brainsmoke/matrixpad/pcb/matrixpad/matrixpad.sch

## KiCad design pcb/matrixpad/matrixpad.sch (2014-07-25)

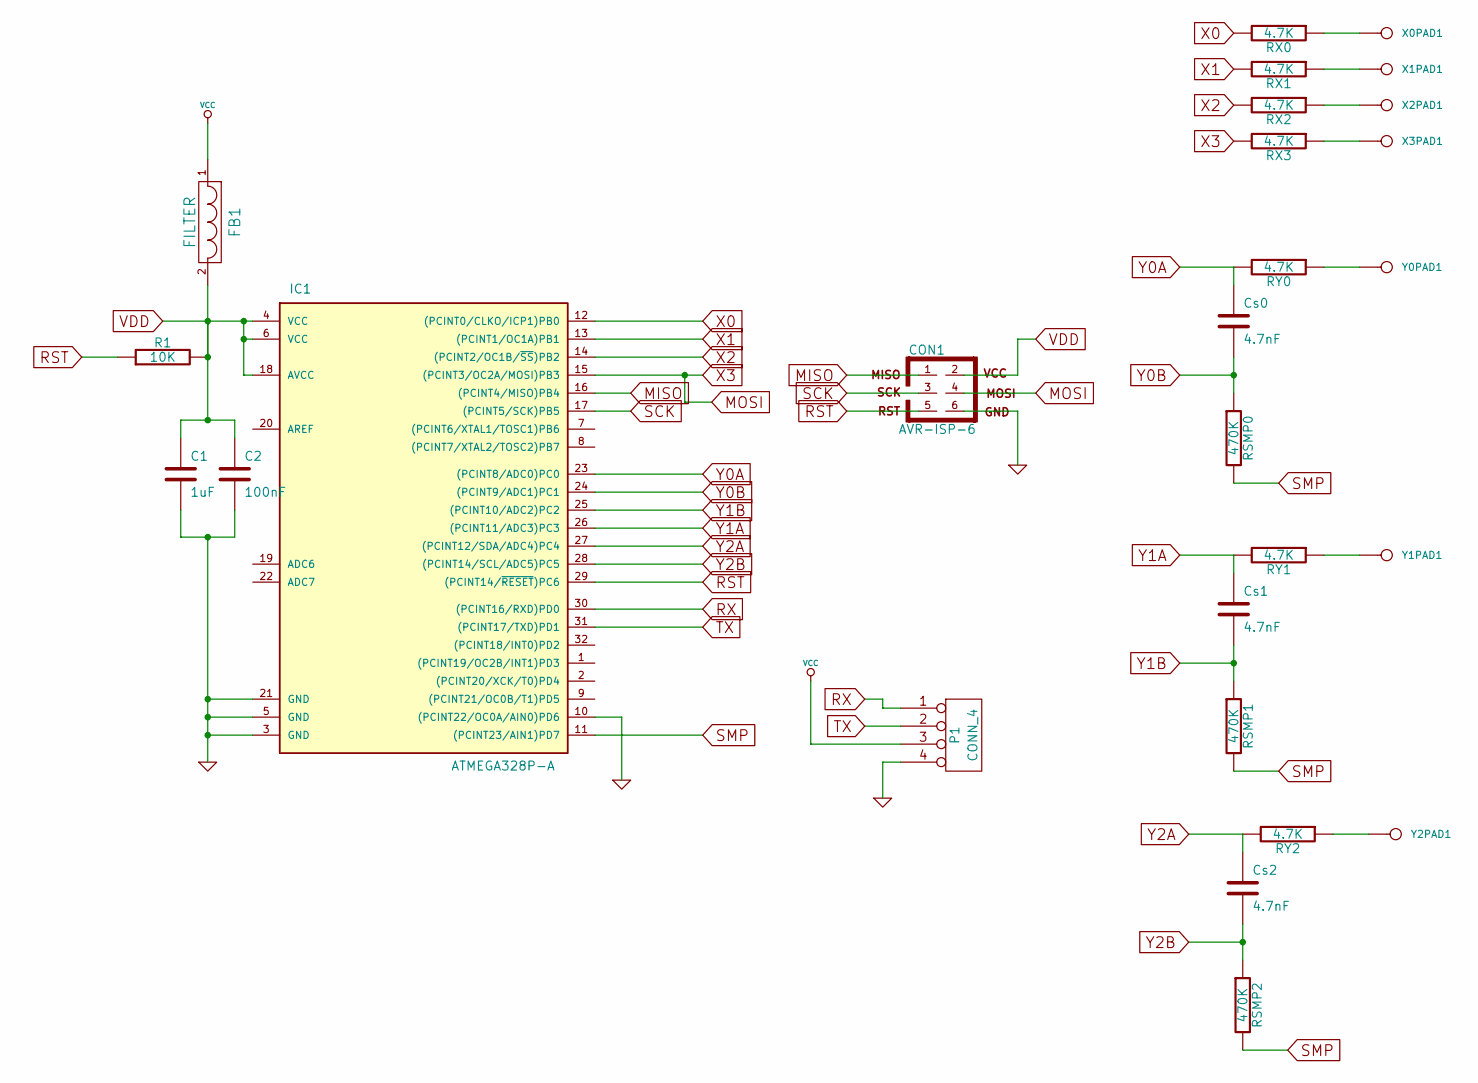
[picture p2: schematic matrixpad.sch]

Parts:
C1: 1uF
C2: 100nF
CON1: AVR-ISP-6
Cs0, Cs1, Cs2: 4.7nF
FB1: FILTER
IC1: ATMEGA328P-A; TQFP32
P1: CONN_4
R1: 10K
RSMP0, RSMP1, RSMP2: 470K
RX0, RX1, RX2, RX3: 4.7K
RY0, RY1, RY2: 4.7K
X0PAD1, X1PAD1, X2PAD1, X3PAD1: CONN_1
Y0PAD1, Y1PAD1, Y2PAD1: CONN_1

Connections:
GND: C1.2, C2.2, CON1.6, IC1.3 (GND), IC1.5 (GND), IC1.10 ((PCINT22/OC0A/AIN0)PD6), IC1.21 (GND), P1.4
MISO: CON1.1, IC1.16 ((PCINT4/MISO)PB4)
MOSI: CON1.4, IC1.15 ((PCINT3/OC2A/MOSI)PB3), RX3.2
unnamed: RX0.1, X0PAD1.1
unnamed: RX1.1, X1PAD1.1
unnamed: RX2.1, X2PAD1.1
unnamed: RX3.1, X3PAD1.1
unnamed: RY0.1, Y0PAD1.1
unnamed: RY1.1, Y1PAD1.1
unnamed: RY2.1, Y2PAD1.1
RST: CON1.5, IC1.29 ((PCINT14/~RESET~)PC6), R1.1
RX: IC1.30 ((PCINT16/RXD)PD0), P1.1
SCK: CON1.3, IC1.17 ((PCINT5/SCK)PB5)
SMP: IC1.11 ((PCINT23/AIN1)PD7), RSMP0.2, RSMP1.2, RSMP2.2
TX: IC1.31 ((PCINT17/TXD)PD1), P1.2
VCC: FB1.1, P1.3
VDD: C1.1, C2.1, CON1.2, FB1.2, IC1.4 (VCC), IC1.6 (VCC), IC1.18 (AVCC), R1.2
X0: IC1.12 ((PCINT0/CLKO/ICP1)PB0), RX0.2
X1: IC1.13 ((PCINT1/OC1A)PB1), RX1.2
X2: IC1.14 ((PCINT2/OC1B/~SS~)PB2), RX2.2
Y0A: Cs0.1, IC1.23 ((PCINT8/ADC0)PC0), RY0.2
Y0B: Cs0.2, IC1.24 ((PCINT9/ADC1)PC1), RSMP0.1
Y1A: Cs1.1, IC1.26 ((PCINT11/ADC3)PC3), RY1.2
Y1B: Cs1.2, IC1.25 ((PCINT10/ADC2)PC2), RSMP1.1
Y2A: Cs2.1, IC1.27 ((PCINT12/SDA/ADC4)PC4), RY2.2
Y2B: Cs2.2, IC1.28 ((PCINT14/SCL/ADC5)PC5), RSMP2.1
